flipdot/drinks-storage-state/src/config.hpp

// Hardware settings
constexpr byte CLOCK_PIN = 14;
constexpr byte DATA_PIN = 12;

// Sample count for median computation
constexpr byte M_SAMPLES = 50;

// MQTT settings
constexpr const char* MQTT_TOPIC = "sensors/cellar/drinks_scale_measurements_raw";

// Network settings
constexpr const char* SSID = "kassel.freifunk.net";
constexpr const char* PASSWORD = "";
constexpr const char* MQTT_HOST = "mqtt.fd";
